laulol07/Licenta/01_Doc/Demo/encoder rotativ 2.jpg

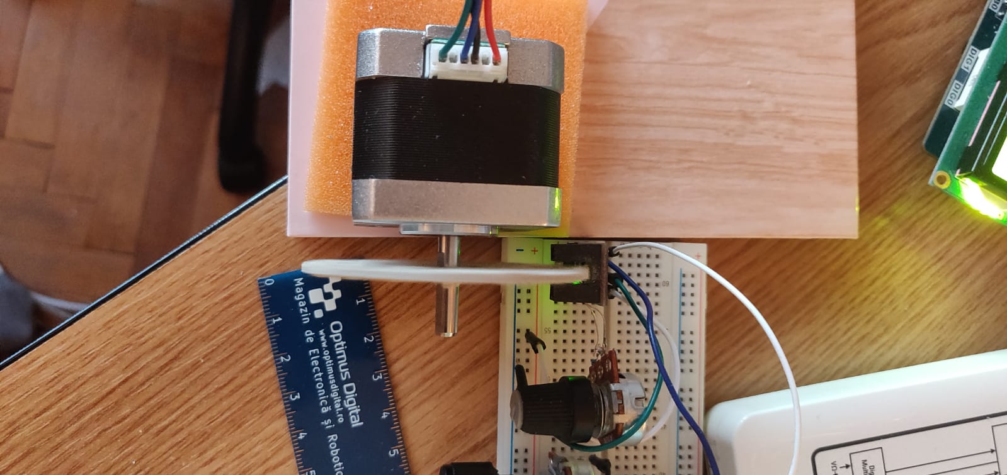
01_Doc/Demo/encoder rotativ 2.jpg
