laulol07/Licenta/01_Doc/Demo/encoder rotativ 3.jpg

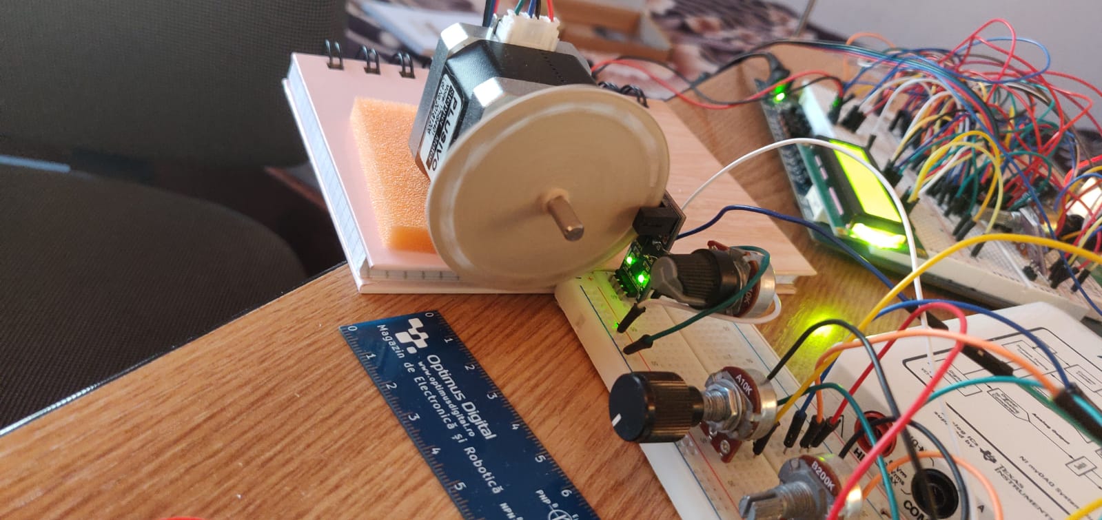
01_Doc/Demo/encoder rotativ 3.jpg
