laulol07/Licenta/01_Doc/Demo/encoder rotativ.jpg

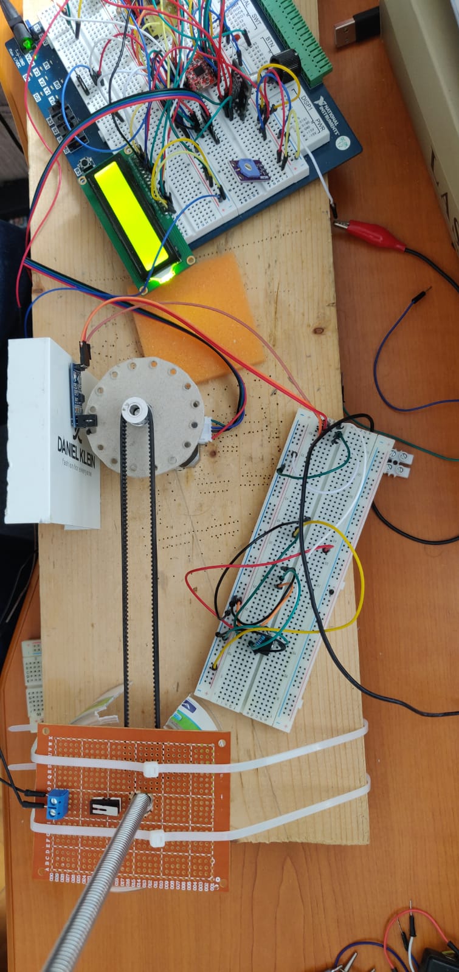
01_Doc/Demo/encoder rotativ.jpg
