laulol07/Licenta/01_Doc/Demo/problema lcd 2.jpg

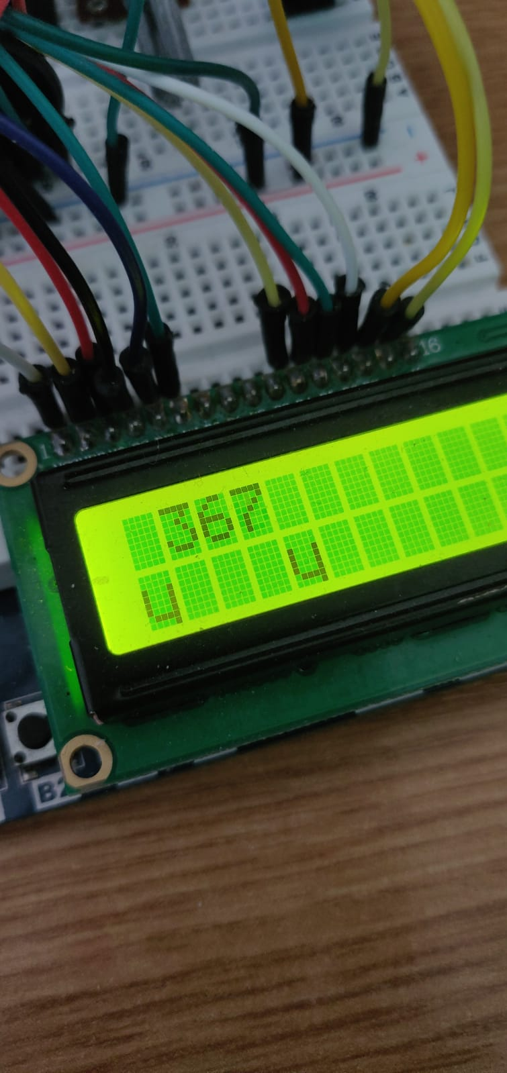
01_Doc/Demo/problema lcd 2.jpg
