laulol07/Licenta/01_Doc/Demo/ultrasonic sensor 2.jpg

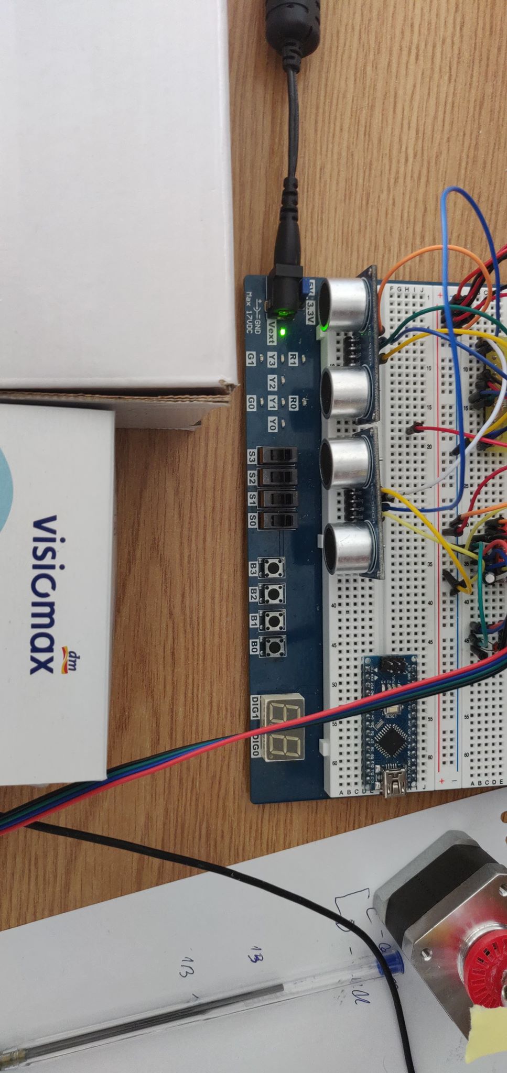
01_Doc/Demo/ultrasonic sensor 2.jpg
