laulol07/Licenta/01_Doc/Demo/ultrasonic sensor.jpg

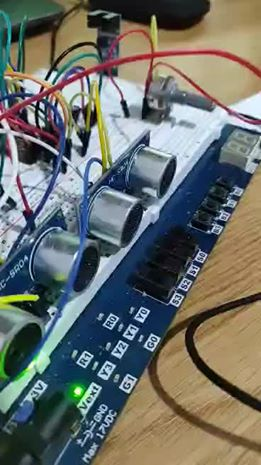
01_Doc/Demo/ultrasonic sensor.jpg
