laulol07/Licenta/01_Doc/Documentatie/Forma de semnal/detectie pahar cu histereza.png

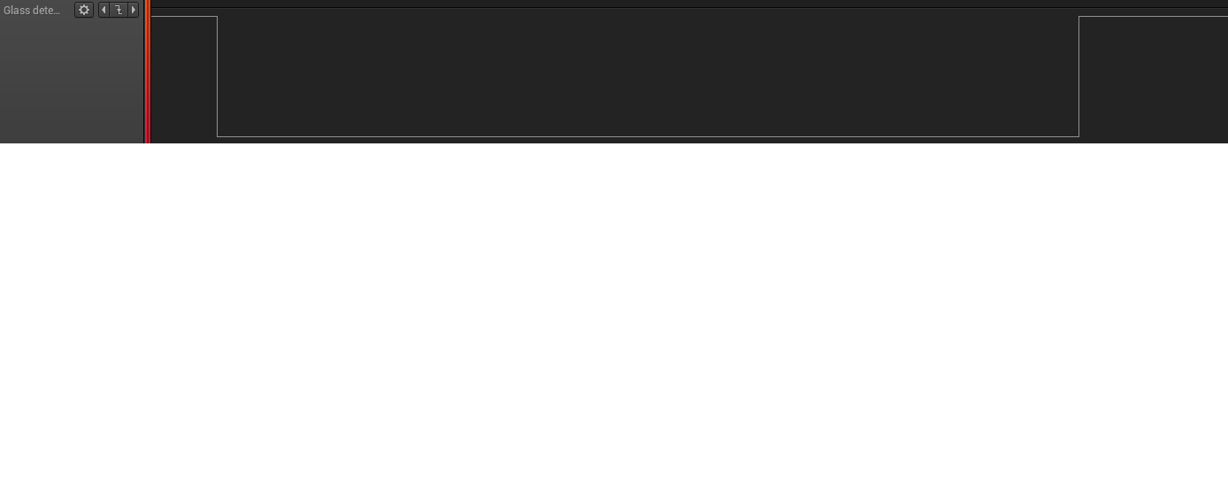
01_Doc/Documentatie/Forma de semnal/detectie pahar cu histereza.png
