laulol07/Licenta/02_SW/01_Dozator.X/02_MCAL/LCD/LCD.h

#ifndef LCD_H_
#define LCD_H_
/**
 * \file       LCD.h
 * \author     Nicoara Ioan
 * \brief      This header provides functions declaration for the LCD 16x2 module
 * \ingroup    GrpName
 *
/*----------------------------------------------------------------------------*/
/*                                  Includes                                  */
/*----------------------------------------------------------------------------*/
#include "../../03_Common/types.h"
/*----------------------------------------------------------------------------*/
/*                             Defines and macros                             */
/*----------------------------------------------------------------------------*/

/*----------------------------------------------------------------------------*/
/*                                 Data types                                 */
/*----------------------------------------------------------------------------*/

/*----------------------------------------------------------------------------*/
/*                 External declaration of global RAM-Variables               */
/*----------------------------------------------------------------------------*/

/*----------------------------------------------------------------------------*/
/*                 External declaration of global ROM-Variables               */
/*----------------------------------------------------------------------------*/

/*----------------------------------------------------------------------------*/
/*                  External declaration of global functions                  */
/*----------------------------------------------------------------------------*/
/**
 * \brief     This function initializes the LCD module
 * \param     None
 * \return    None 
 * \pre       -
 * \post      -
 */
 
void LCD_vInit(void);

/**
 * \brief     Cyclic function that is called one of the OS tasks
 * \param     None
 * \return    None 
 * \pre       -
 * \post      -
 */
void LCD_vMainFunction(void);

/**
 * \brief     This function sends a string to the display;
 * \param     StringToBeSent - Is  a pointer to an array representing the string that needs to be sent;
 * \param     startingPoint - Represents the index where the first char of StringToBeSent will be put into the LCD's array;
 * \param     length - Represents the number of characters of StringToBeSent;
 * \return    None 
 * \pre       -
 * \post      -
 */

void LCD_vWriteString(uint8_t * StringToBeSent, uint8_t startingPoint, uint8_t length);

void LCD_vWriteNumber(uint16_t NumberToBeSent, uint8_t startingPoint, uint8_t length);
#endif
